AFUDIrk/CADDeck/images/49E_Verkabeln.png

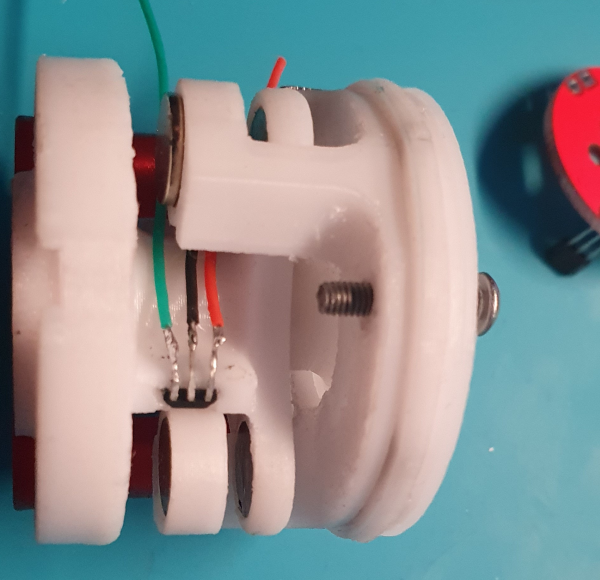
images/49E_Verkabeln.png
