AFUDIrk/CADDeck/images/Bohrungen.png

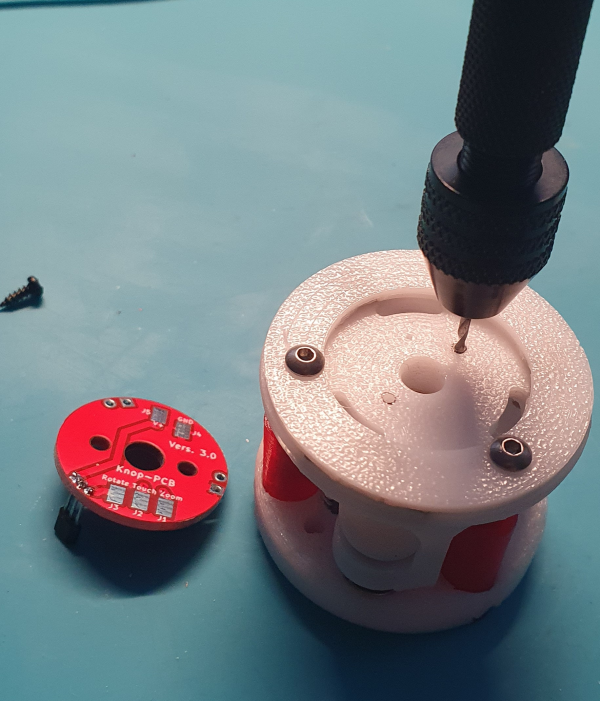
images/Bohrungen.png
