AFUDIrk/CADDeck/images/Bohrungen_anzeichnen.png

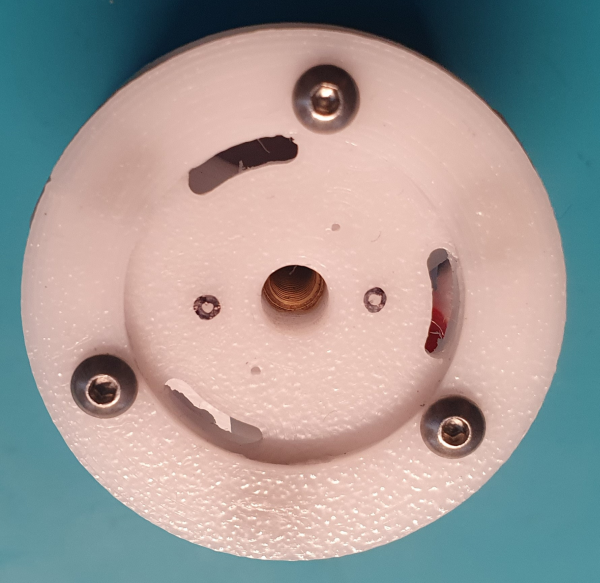
images/Bohrungen_anzeichnen.png
