AFUDIrk/CADDeck/images/BottomView.png

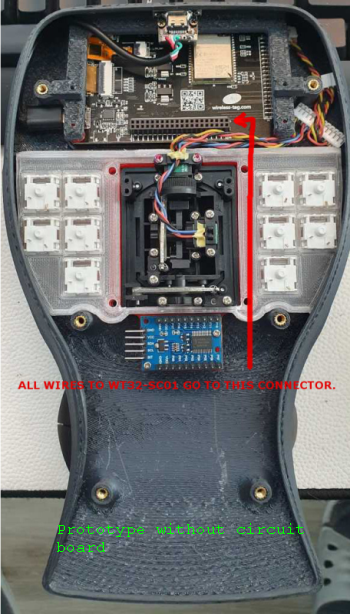
images/BottomView.png
