AFUDIrk/CADDeck/images/CADDeck.png

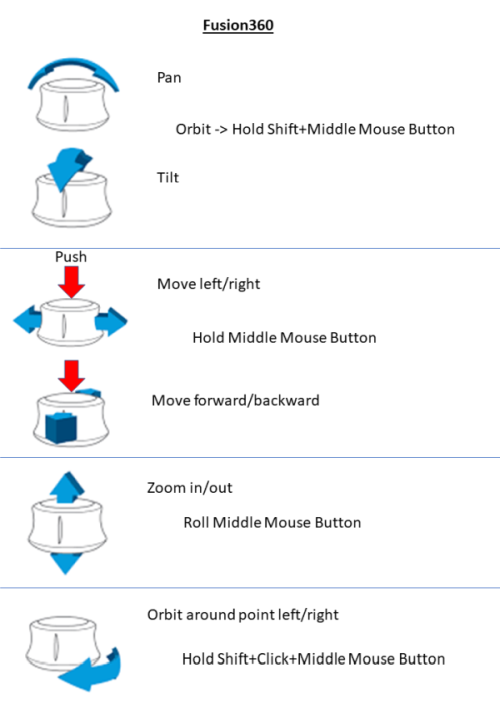
images/CADDeck.png
