AFUDIrk/CADDeck/images/FrontBottomView.png

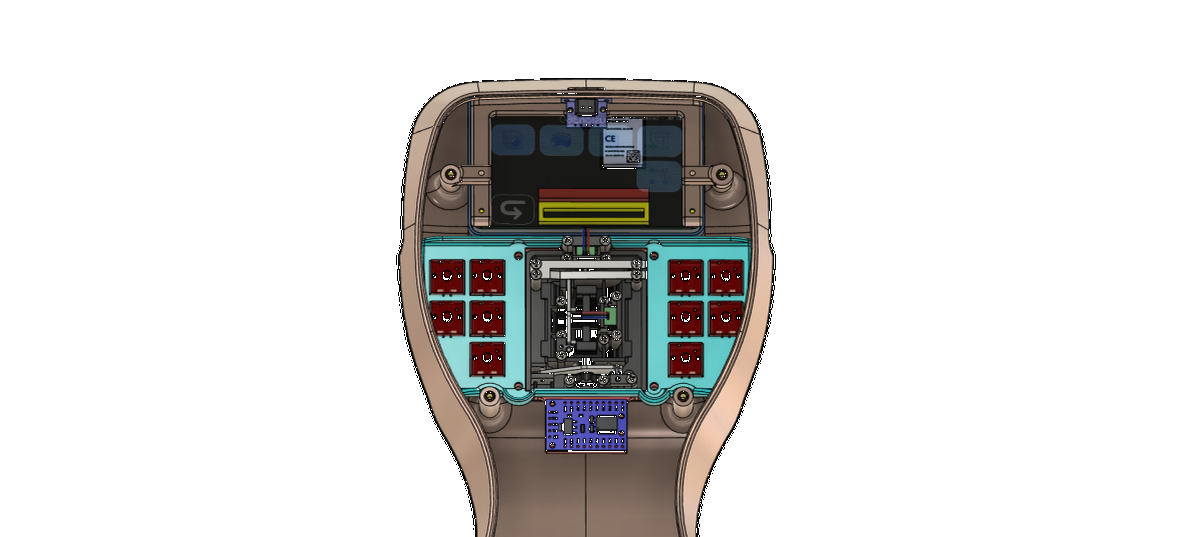
images/FrontBottomView.png
