AFUDIrk/CADDeck/images/fusion360.png

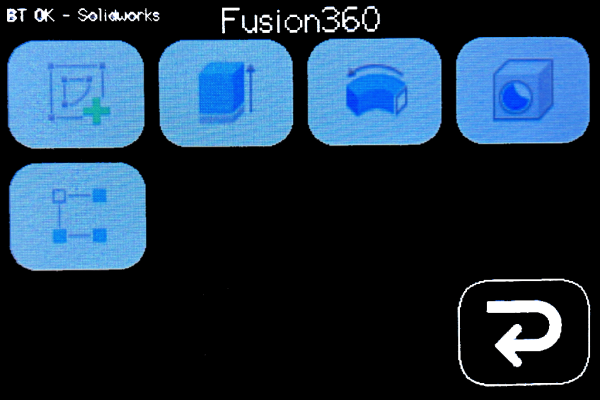
images/fusion360.png
