AFUDIrk/CADDeck/images/Gewichte.png

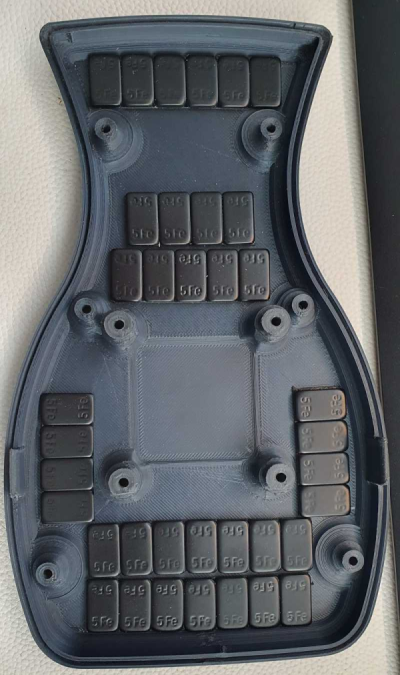
images/Gewichte.png
