AFUDIrk/CADDeck/images/GrundplattemitLangmutter.png

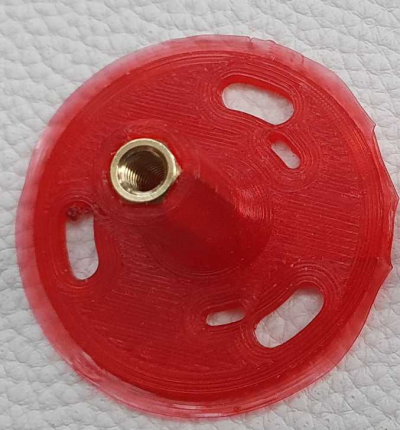
images/GrundplattemitLangmutter.png
