AFUDIrk/CADDeck/images/Hall. Zoom.png

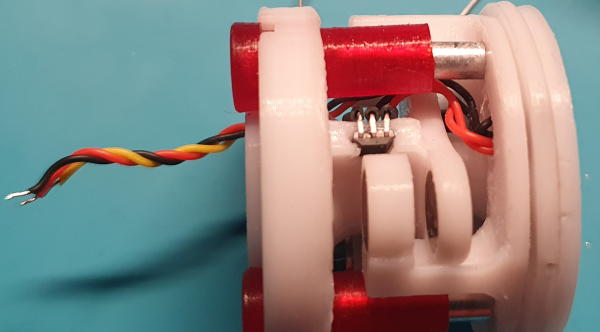
images/Hall. Zoom.png
