AFUDIrk/CADDeck/images/Hallsensor Position.png

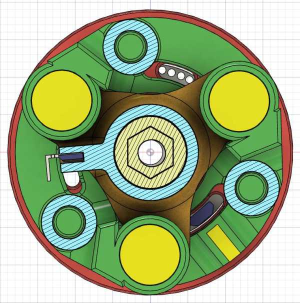
images/Hallsensor Position.png
