AFUDIrk/CADDeck/images/Hallsensorplatine.png

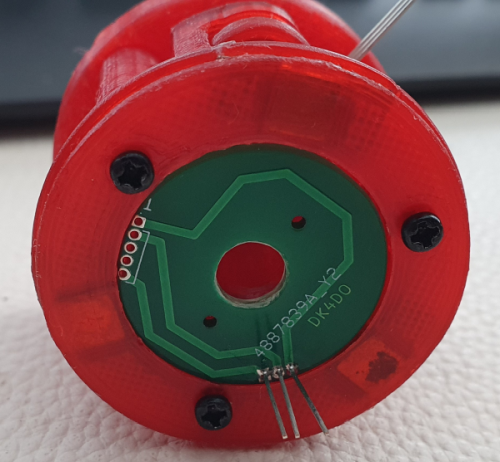
images/Hallsensorplatine.png
