AFUDIrk/CADDeck/images/Knopf.png

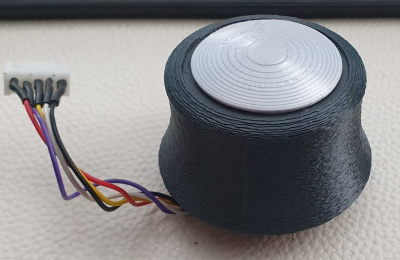
images/Knopf.png
