AFUDIrk/CADDeck/images/Magnetanordnung Rotate.png

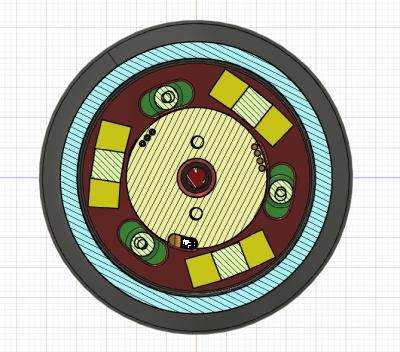
images/Magnetanordnung Rotate.png
