AFUDIrk/CADDeck/images/Magnetanordnung.png

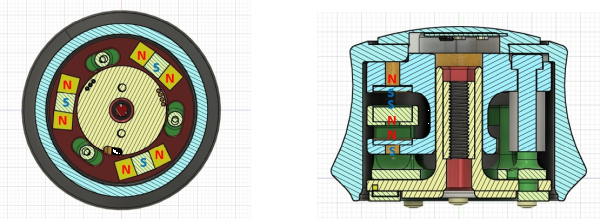
images/Magnetanordnung.png
