AFUDIrk/CADDeck/images/Platine_oben.png

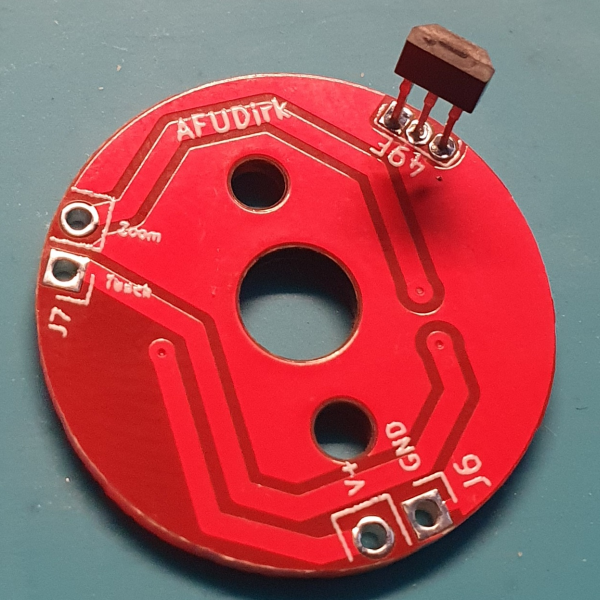
images/Platine_oben.png
