AFUDIrk/CADDeck/images/Schaumstoff.png

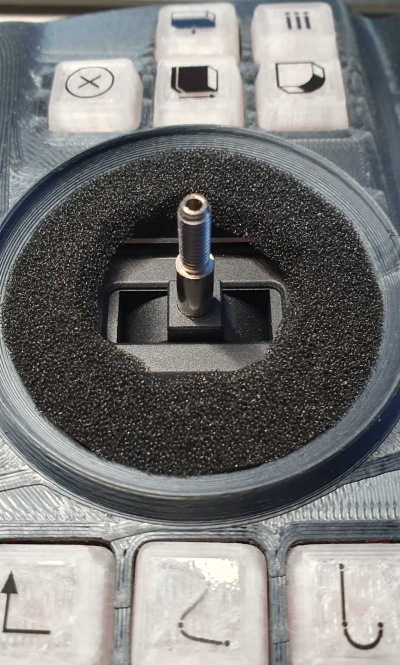
images/Schaumstoff.png
