AFUDIrk/CADDeck/images/Screen3x4Home.png

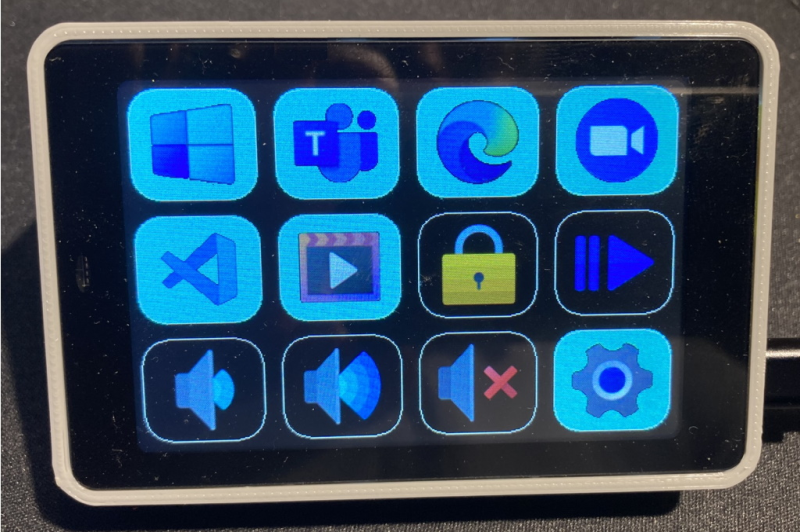
images/Screen3x4Home.png
