AFUDIrk/CADDeck/images/SupportGrungplatte.png

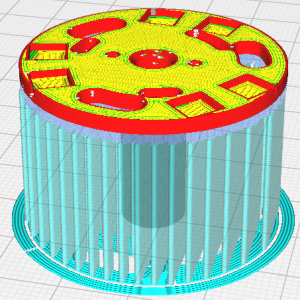
images/SupportGrungplatte.png
