AFUDIrk/CADDeck/images/SupportKreuz.png

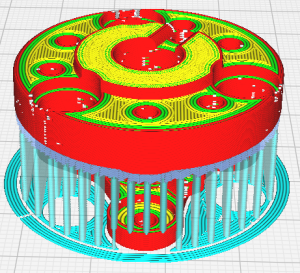
images/SupportKreuz.png
