AFUDIrk/CADDeck/images/SupportMagnethalter.png

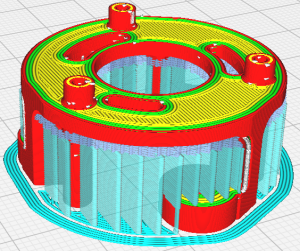
images/SupportMagnethalter.png
