AFUDIrk/CADDeck/images/Supportoben.png

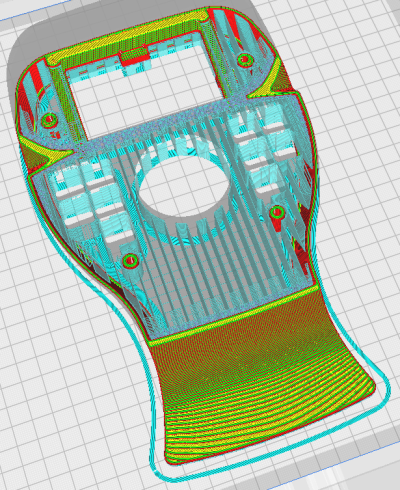
images/Supportoben.png
