AFUDIrk/CADDeck/images/Tp223.png

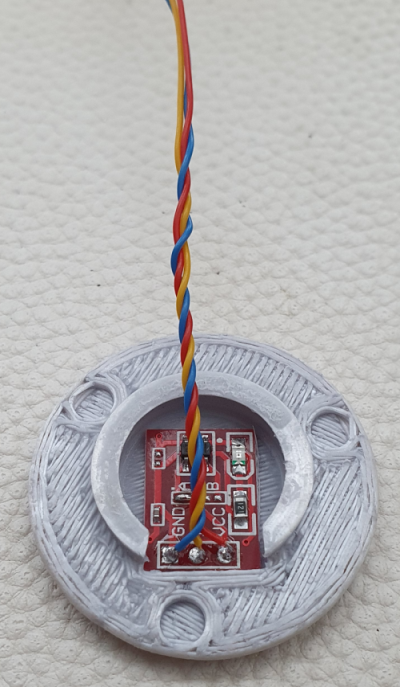
images/Tp223.png
