AFUDIrk/CADDeck/hardware/Case/Kreutz.3mf

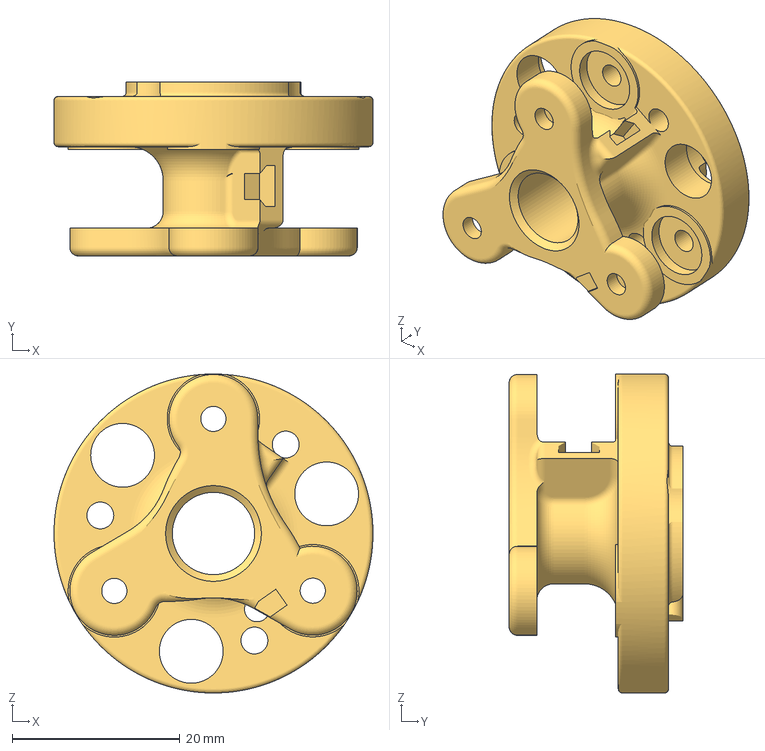
[picture p67: CAD file, 2023-05-01]
hardware/Case/Kreutz.3mf
38.0 x 20.7 x 38.0 mm
