AFUDIrk/CADDeck/hardware/Case/Hülse_3x.3mf

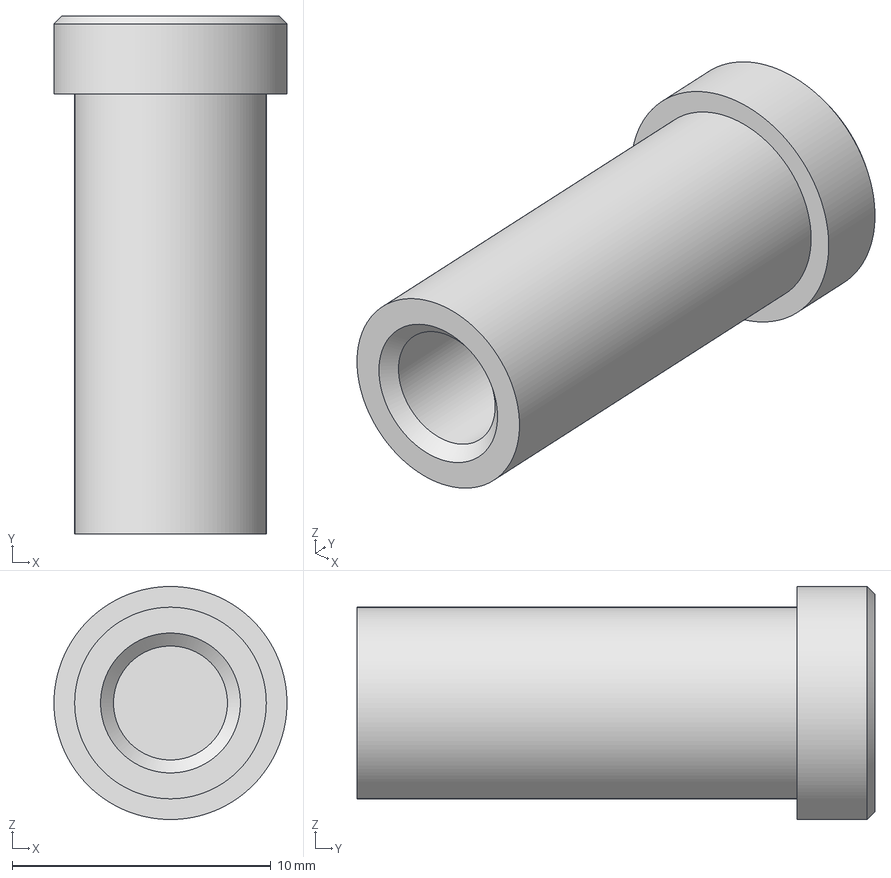
[picture p68: CAD file, 2023-04-21]
hardware/Case/Hülse_3x.3mf
9.00 x 20.0 x 9.00 mm
