AFUDIrk/CADDeck/hardware/Case/Kabelklemme.3mf

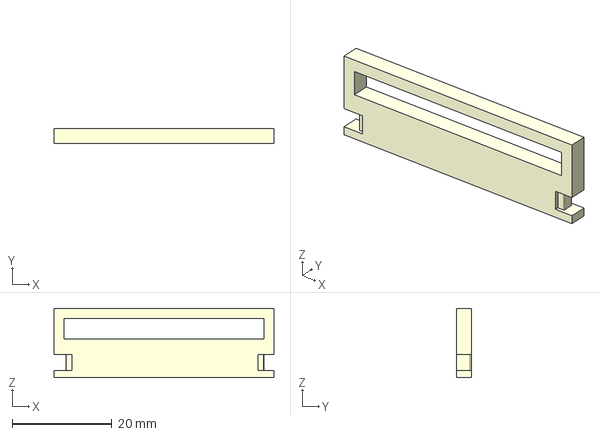
[picture p69: CAD file, 2023-03-21]
hardware/Case/Kabelklemme.3mf
44.1 x 3.00 x 13.8 mm
