AFUDIrk/CADDeck/hardware/Case/Steckerhalter.3mf

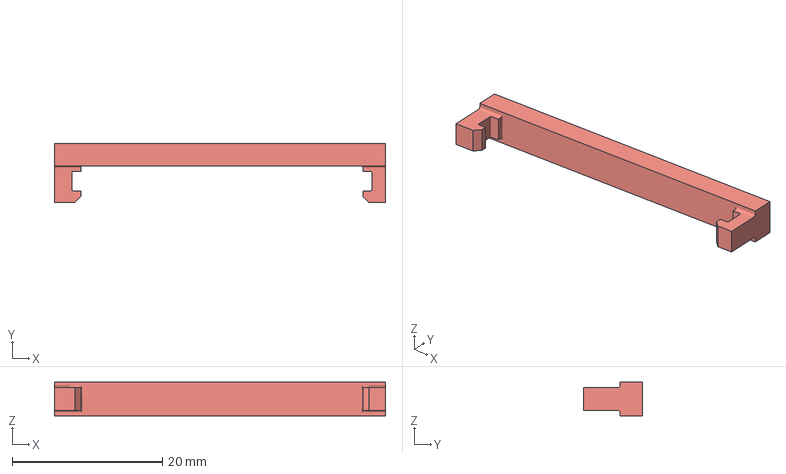
[picture p70: CAD file, 2023-03-21]
hardware/Case/Steckerhalter.3mf
44.0 x 7.86 x 4.50 mm
