AFUDIrk/CADDeck/hardware/Case/Abstandshalter_2x.3mf

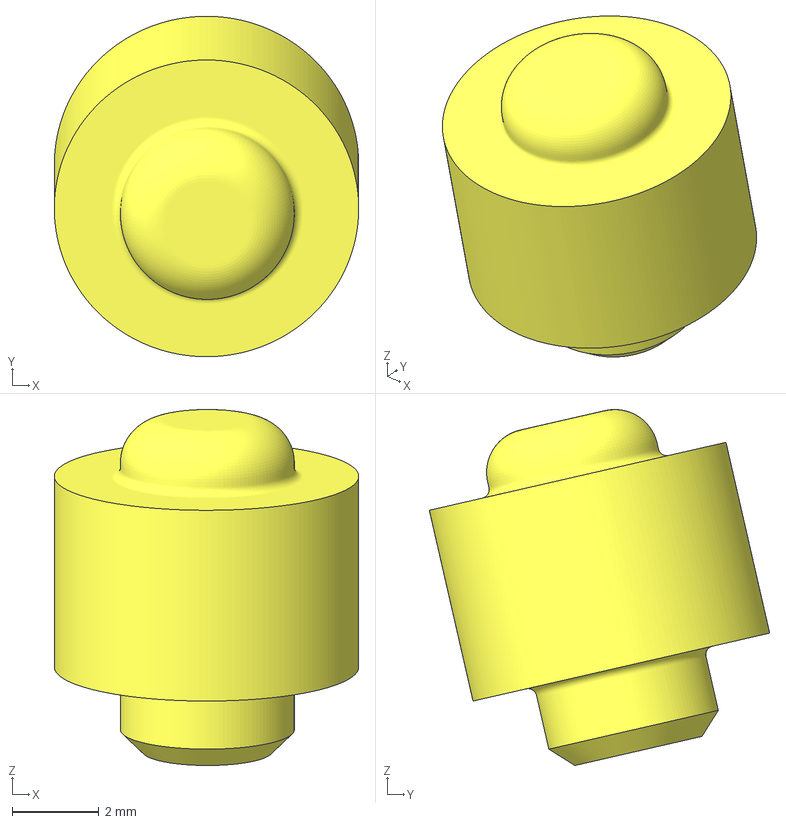
[picture p71: CAD file, 2023-03-17]
hardware/Case/Abstandshalter_2x.3mf
7.00 x 7.83 x 8.19 mm
