AFUDIrk/CADDeck/hardware/Case/Taster Kappe gerade 6x.3mf

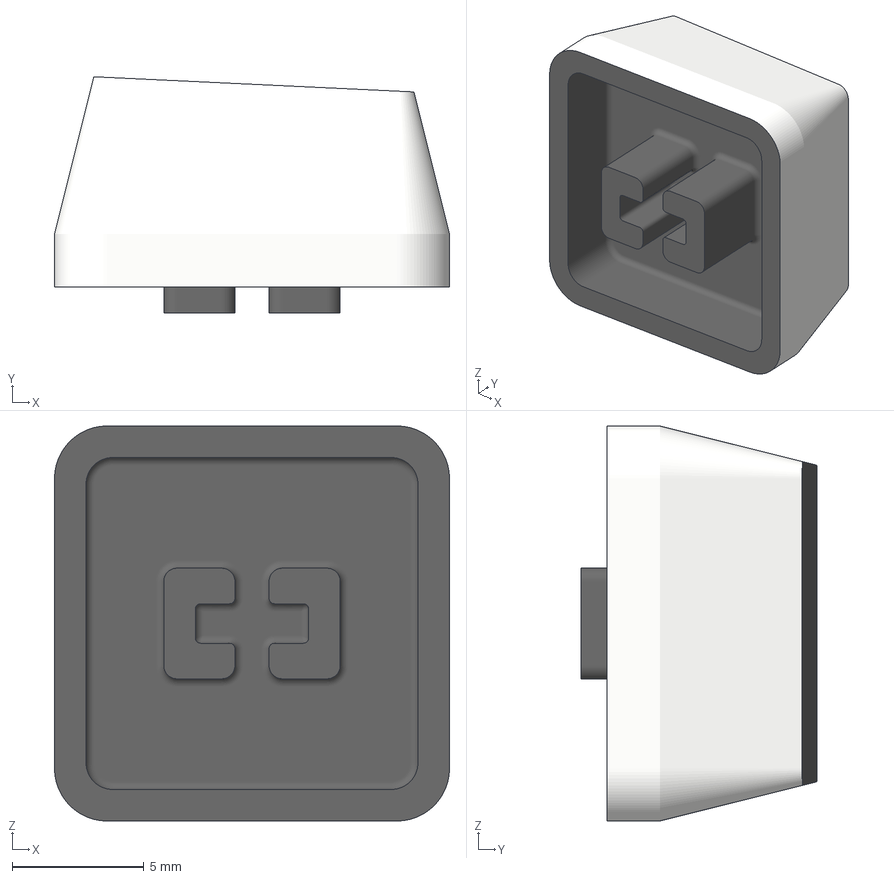
[picture p72: CAD file, 2023-03-17]
hardware/Case/Taster Kappe gerade 6x.3mf
15.0 x 8.98 x 15.0 mm
