AFUDIrk/CADDeck/hardware/Case/Taster Kappe schräg 4x.3mf

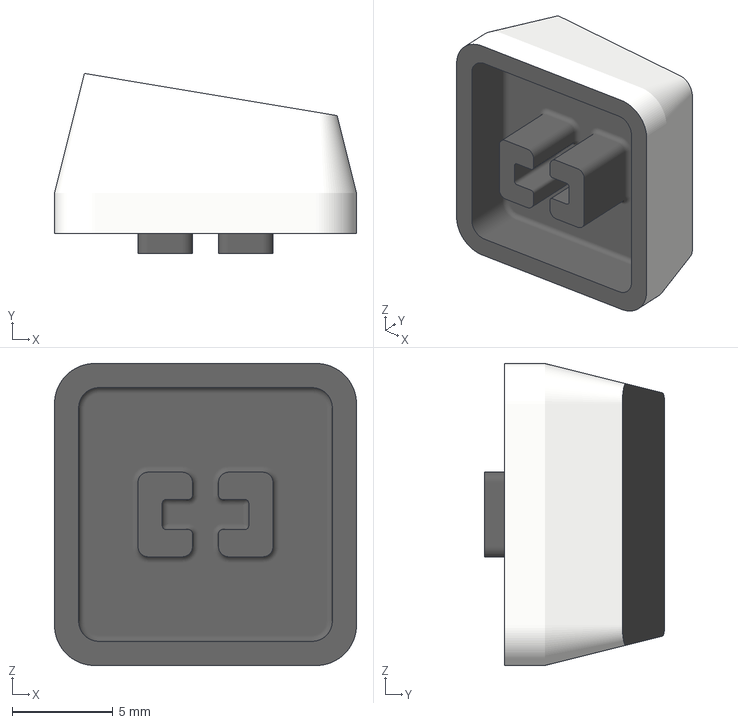
[picture p73: CAD file, 2023-03-17]
hardware/Case/Taster Kappe schräg 4x.3mf
15.0 x 8.95 x 15.0 mm
