AFUDIrk/CADDeck/hardware/Case/Dichtung_TPU Displ..3mf

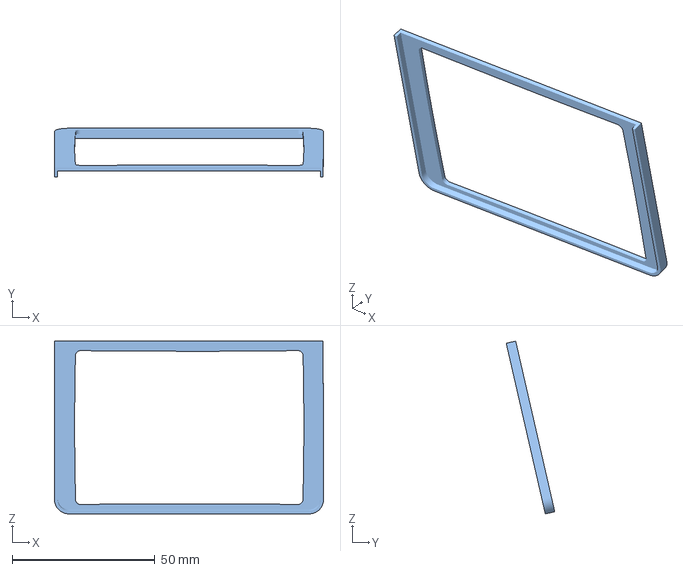
[picture p74: CAD file, 2023-03-16]
hardware/Case/Dichtung_TPU Displ..3mf
94.1 x 17.0 x 60.4 mm
