AFUDIrk/CADDeck/hardware/Case/Rad.3mf

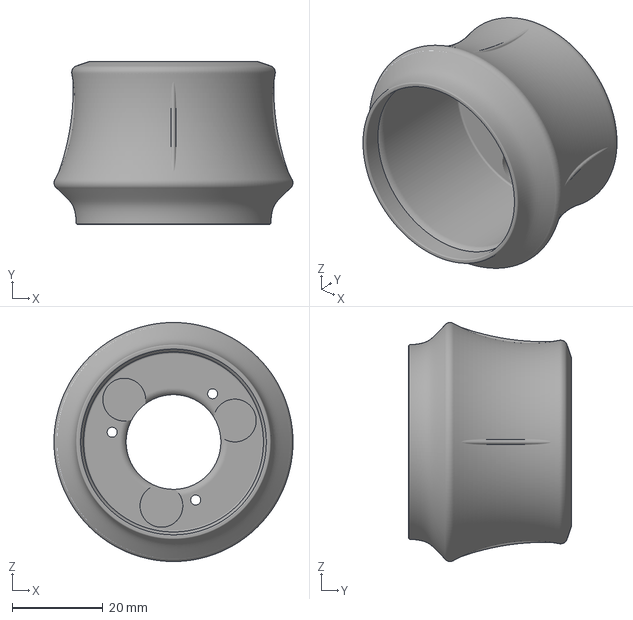
[picture p75: CAD file, 2023-03-16]
hardware/Case/Rad.3mf
52.5 x 35.8 x 52.5 mm
